vives-projectwerk-2-2020/SolarPCB-BUG-/Develop board/Solar Charger Shield v2.2 (deze is niet in het eigen ontwerp gebruikt)/Solar Charger Shield v2.2 manual.pdf

# Solar Charger Shield V2.2

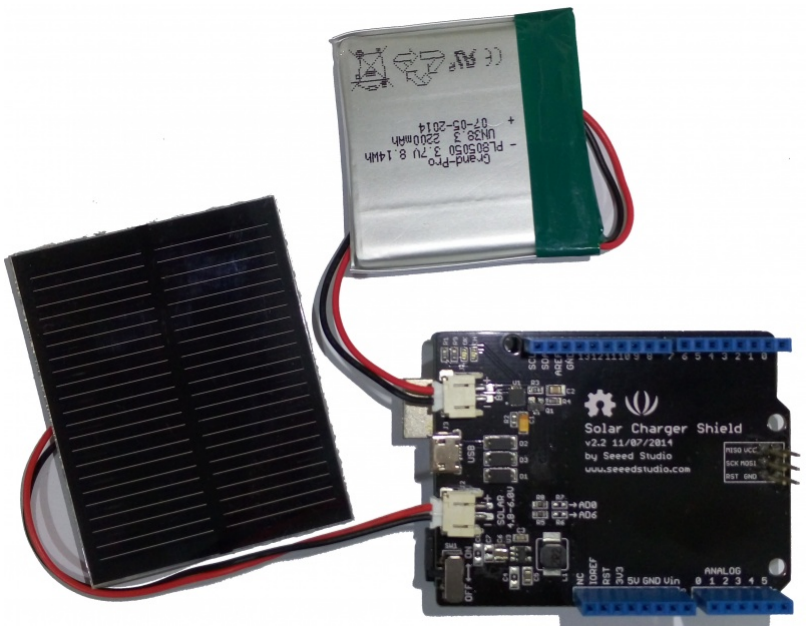
[picture p15: figure]

The solar charger is a stackable shield to Arduino compatible platforms, enables adaptive battery power and act as energy harvester for in-field charging. You may use various batteries that has the voltage of 3.0V-4.2V to shift up for 5V output, or put on Li-ion battery and solar panel to form an autonomous sensor unit. The maximum current provided by the board can get up to 600mA. An usb connector is also useful to charge the battery.

## Features

- Output Disconnect
- Short circuit protection
- 3W Output Power when connecting battery
- Continuous Charge Current Up to 900mA
- Battery status indication ( Red : Charging , Green: Charged )
- Micro-USB Connector

## Specification

- Battery input voltage: 3.0~4.5V
- USB input voltage: 4.75~5.25V
- Solar input voltage: 4.8~6V
- Maximum Output Power(with battery): 3W(600mA@5V)

- Ripple voltage：<100mV @ 500mA
- Dimensions: 68*53mm

## Applications

- Wireless sensor unit
- Solar charge
- Tweet-a-volt-arduino

## Information on use of Solar panels for charging

1) The solar charger shield produces charges under sunlight and light from filament bulbs. Its function is more effective in the former than in the latter. Solar panels require invisible radiations namely ultraviolet and infrared radiations for producing current.
2) In order to test the system under filament bulb, hold the solar panel at a distance, less than 20cm(< 0.5 feet). However, the charging may not be effective under filament bulbs.
3) Place the solar panel at an angle such that the maximum amount of sunlight is incident on it.
4) Protect the solar panel from excessive exposure to water/water vapors. This may oxidize the surface of the solar panel and reduce its performance.
5) The Solar panel usually comes with a protective transparent sheet of cover. Remove the transparent plastic sheet for better performance of the solar panel.
6) Protect the surface of the solar panel from scratches

## Caution

1) The solar charger shield is designed to protect any potential short circuit. However care must be taken to avoid any such situations.
2) The solar shield should not be operated at voltages greater than 5V

## Usage

1) Connect the Solar panel and the Li-Pol battery in their designated places as shown in the figure below:

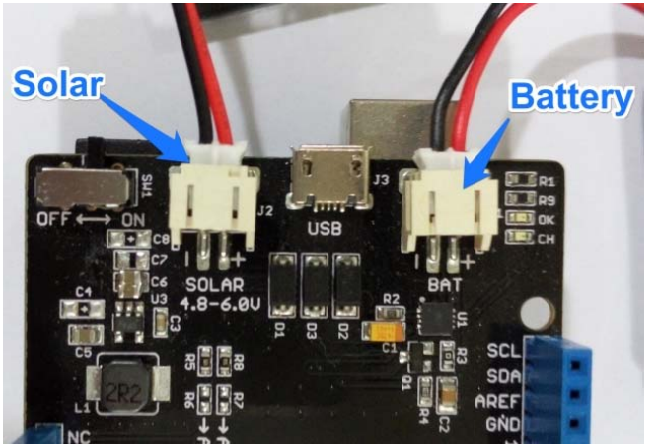
[picture p16: figure]

Solar

2) Pl
solar
3) En

r_Charger_

lace the sola
r panels" sec

nsure that th

Shield_v2.2

ar under sun
ction

he charging

2_inputs.jpg

nlight or fila

(Red) light

ament bulbs

t glows as s

as mention

hown in the

ned in the "I

e figure belo

Information

ow:

for using

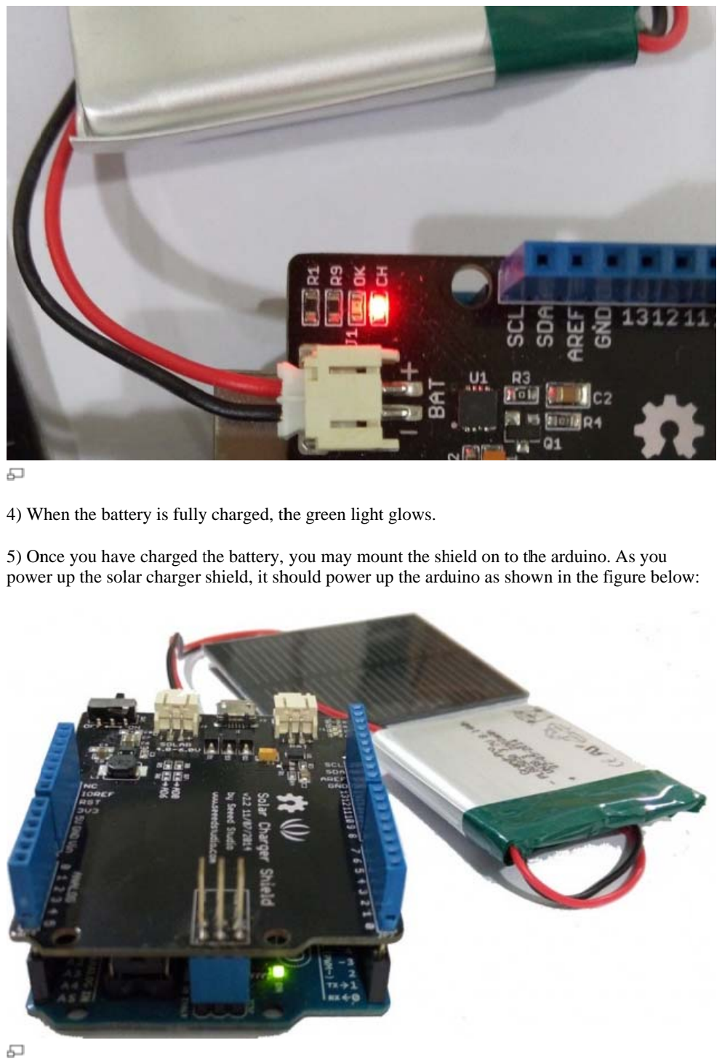
[picture p17: page 4]

4) W
5) On
powe

When the bat

nce you hav
er up the so

ttery is fully

ve charged t
lar charger

charged, th

he battery,
shield, it sh

e green lig

you may m
hould power

ght glows.

mount the sh
r up the ard

hield on to th
uino as show

he arduino.
own in the fi

As you
gure below:

## Tes

Shor

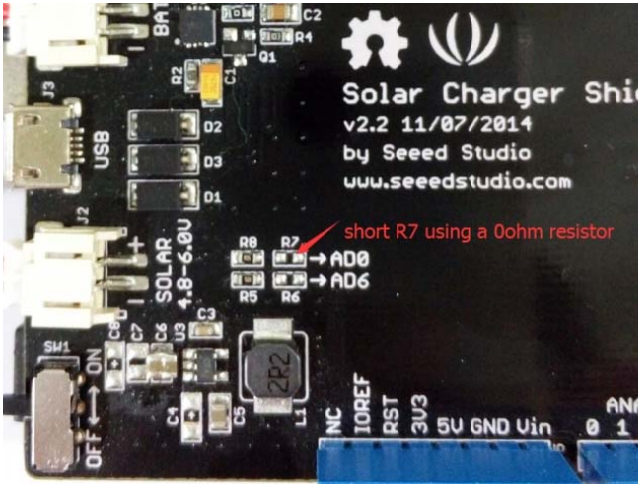
[picture p18: figure]

Img

Prog

You

/*
Sol lar charge | er shield | voltage m measuremen | nt example | e. Connect | t VBAT pin | n to analo | og
pin | A0.
The e pin meas | sures 2.0 | V when no ot under d | direct exp | posre to s | sunlight a | and 5V whe | n
expo osed to su | unlight.

Thi

*/

// T These cons | stants won | n't change | e. They'r | re used to | • give nam | mes
// t to the pin | ns used:
cons st int ana | alogInPin | | = A0; // / Analog i | input pin | | that the | VBAT pin | is
atta ached to

## sting th

rt R7 using a

Solar_Char

gramming

can measur

is example

## he solar

a 0ohm resi

rger_Shield_

g Example

re the voltag

e code is

## shield w

istor as show

_v2.2_short

e

ge of Batter

in the pu

## with a s

wn in the fig

tR7.jpg

ry using the

ublic doma

## simple a

gure:

following e

ain.

## arduino

example:

## o progr

am

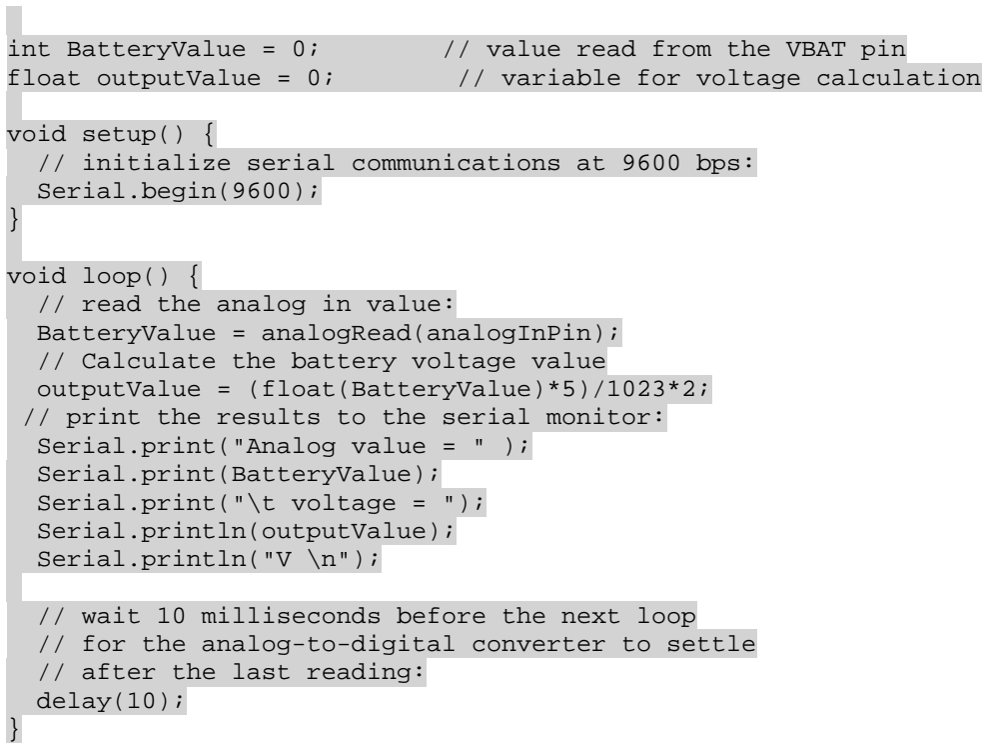
[picture p19: figure]
void setup() {; Serial.begin(9600);; void loop() { // read the analog in value: BatteryValue = analogRead(analogInPin); // Calculate the battery voltage value; Serial.print("Analog value = " ); Serial.print(BatteryValue); Serial.print("\t voltage = "); Serial.println(outputValue); Serial.println("V \n");; // after the last reading: delay(10);

int BatteryValue = 0; | // value read from the VBAT pin
float outputValue = 0; | // variable for voltage calculation

// initialize serial communications at 9600 bps:

outputValue = (float(BatteryValue)*5)/1023*2; // print the results to the serial monitor:

// wait 10 milliseconds before the next loop // for the analog-to-digital converter to settle
